PatchBOTS/L337/STLs/V2/BASE_BaseandNeck.STL

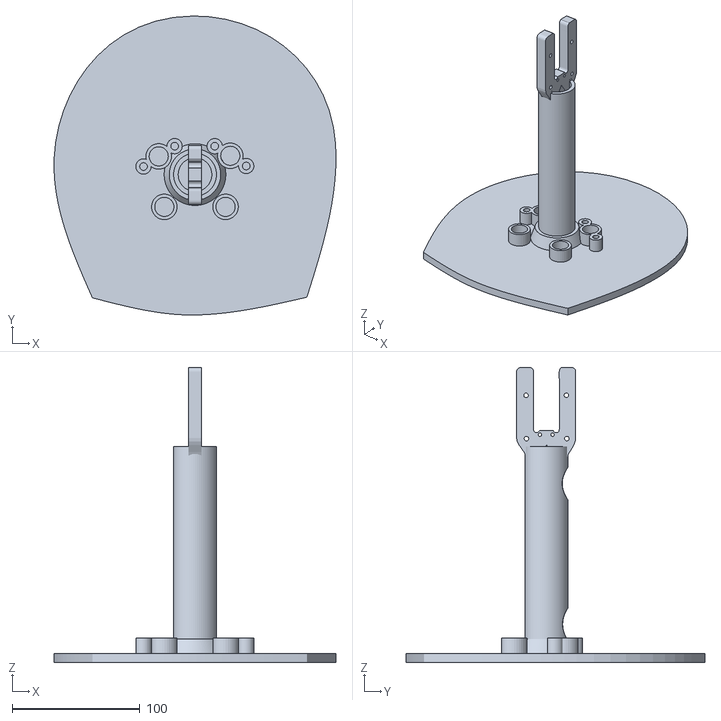
[picture p15: CAD file, 2018-09-10]
STLs/V2/BASE_BaseandNeck.STL
220.7 x 234.0 x 231.1
