PatchBOTS/L337/STLs/PartsChanging/HEAD_ELECTRICAL_MountCover.STL

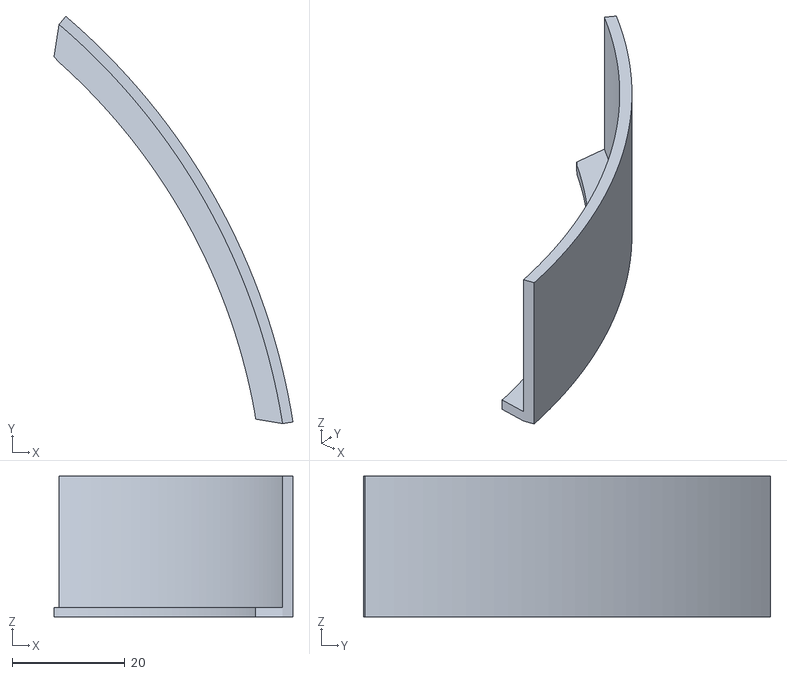
[picture p16: CAD file, 2018-06-11]
STLs/PartsChanging/HEAD_ELECTRICAL_MountCover.STL
42.4 x 72.2 x 24.9
