PatchBOTS/L337/STLs/V2/HEAD_ELECTRICAL_SpeakerMount.STL

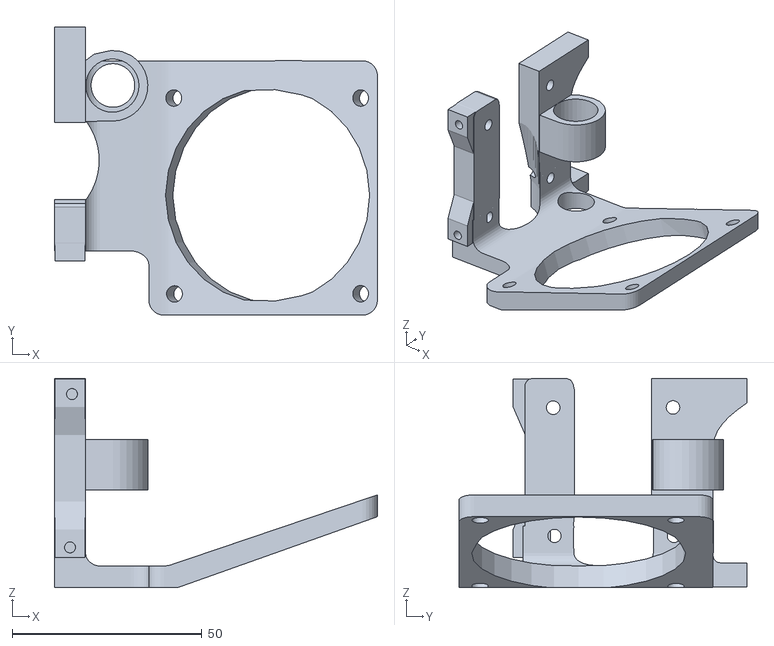
[picture p17: CAD file, 2018-09-10]
STLs/V2/HEAD_ELECTRICAL_SpeakerMount.STL
85.2 x 76.1 x 55.2
