PatchBOTS/L337/STLs/HEAD_AESTHETIC_EarGreebly.STL

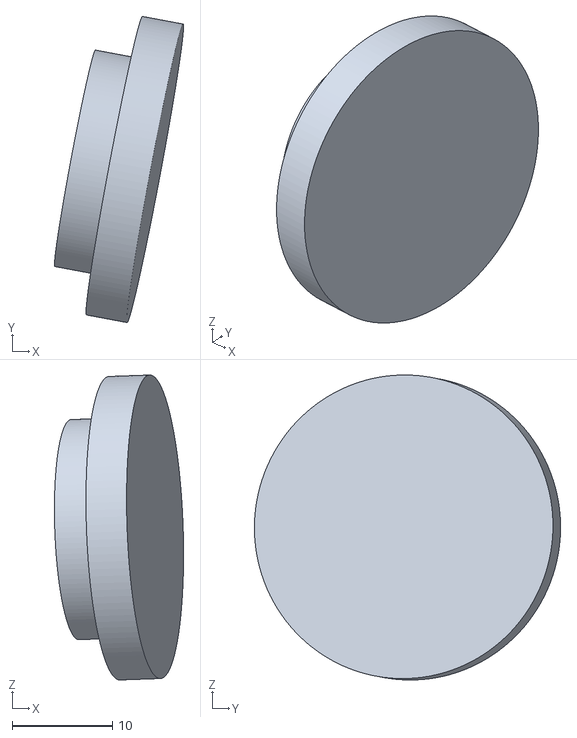
[picture p18: CAD file, 2018-06-11]
STLs/HEAD_AESTHETIC_EarGreebly.STL
12.9 x 30.5 x 30.4
