PatchBOTS/L337/STLs/HEAD_LID_Cap_T2.STL

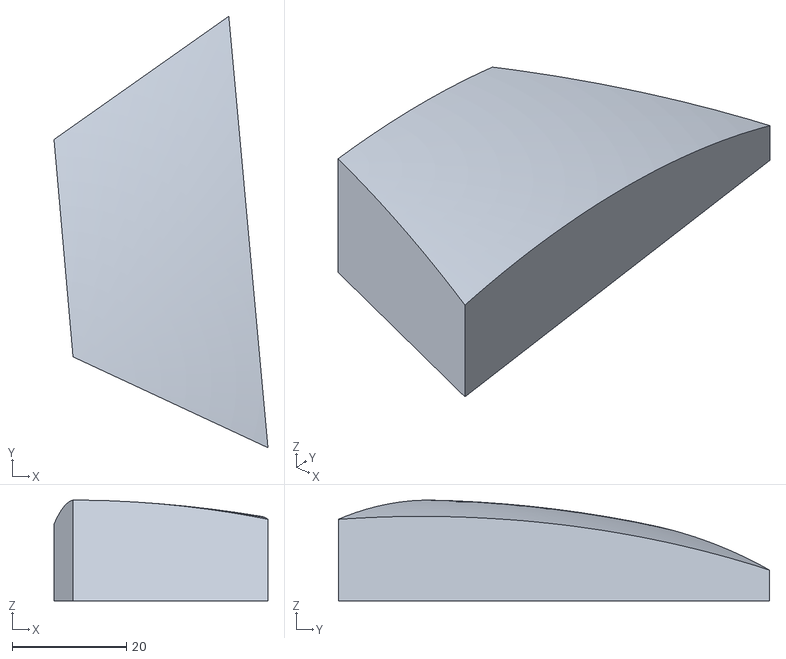
[picture p19: CAD file, 2018-06-11]
STLs/HEAD_LID_Cap_T2.STL
37.5 x 75.5 x 17.7
