PatchBOTS/L337/STLs/PartsChanging/HEAD_ELECTRICAL_InternalHoop.STL

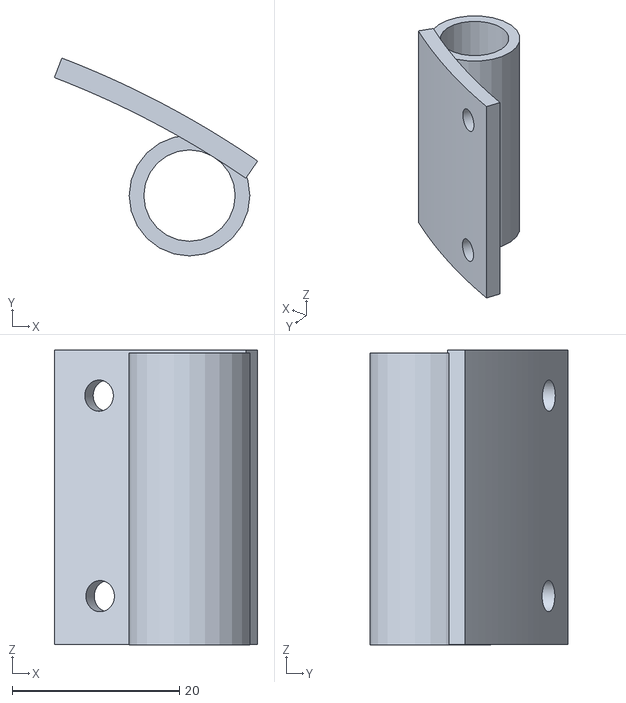
[picture p20: CAD file, 2018-06-11]
STLs/PartsChanging/HEAD_ELECTRICAL_InternalHoop.STL
24.3 x 23.7 x 35.3
