PatchBOTS/L337/STLs/HEAD_AESTHETIC_Eye.STL

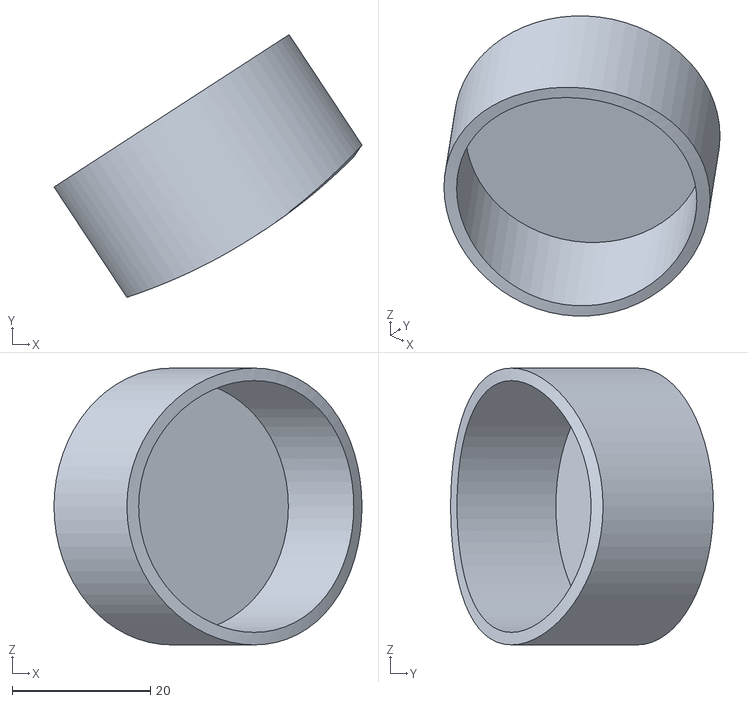
[picture p21: CAD file, 2018-06-11]
STLs/HEAD_AESTHETIC_Eye.STL
44.6 x 38.1 x 40.1
