PatchBOTS/L337/STLs/PartsChanging/HEAD_ELECTRICAL_SpeakerMount_CS.STL

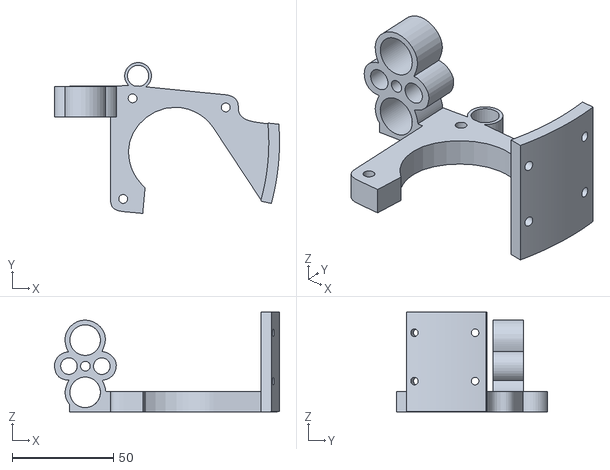
[picture p22: CAD file, 2018-06-11]
STLs/PartsChanging/HEAD_ELECTRICAL_SpeakerMount_CS.STL
111.0 x 74.5 x 49.3
