PatchBOTS/L337/STLs/HEAD_LID_Cap_T1.STL

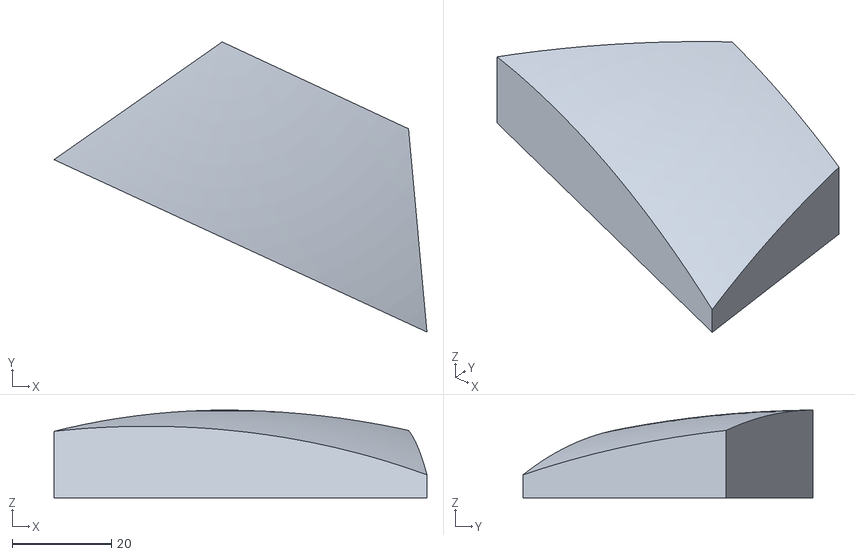
[picture p23: CAD file, 2018-06-11]
STLs/HEAD_LID_Cap_T1.STL
75.2 x 58.5 x 17.7
