PatchBOTS/L337/STLs/BASE_CollarGreebly.STL

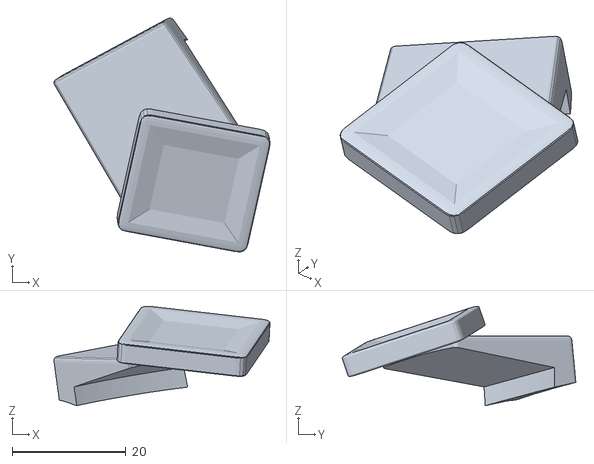
[picture p24: CAD file, 2018-06-11]
STLs/BASE_CollarGreebly.STL
38.0 x 41.2 x 17.5
