PatchBOTS/L337/STLs/HEAD_LID_Cap_T3.STL

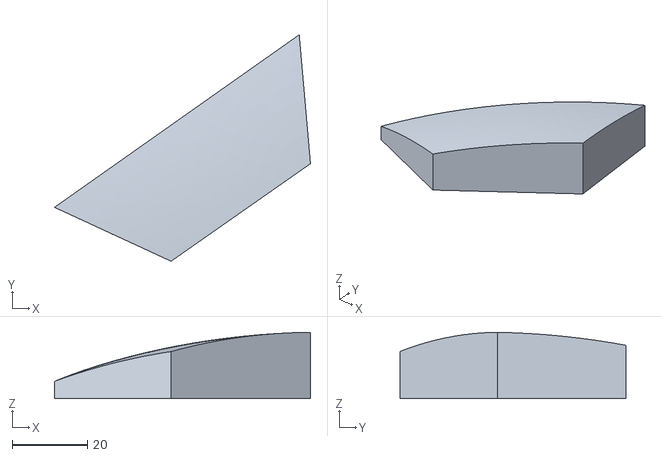
[picture p25: CAD file, 2018-06-11]
STLs/HEAD_LID_Cap_T3.STL
68.0 x 60.2 x 17.6
