PatchBOTS/L337/STLs/HEAD_ELECTRICAL_NeoDiffusex2.STL

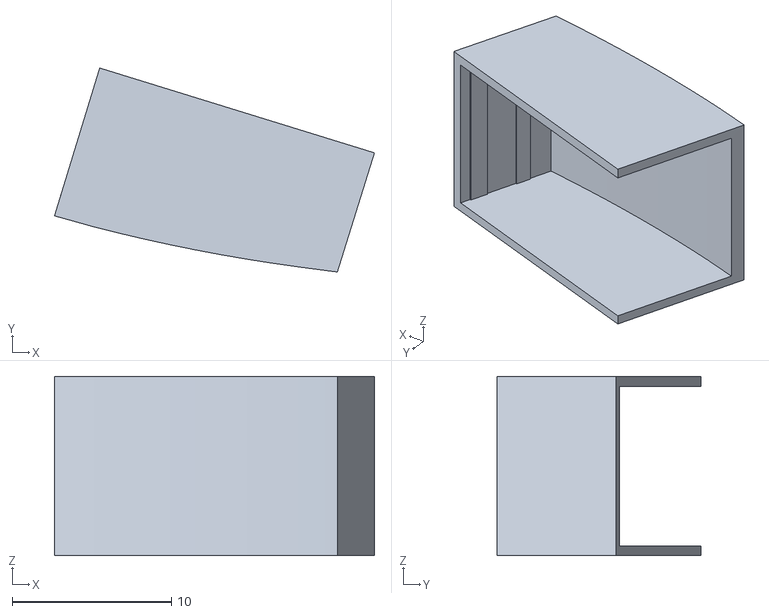
[picture p26: CAD file, 2018-06-11]
STLs/HEAD_ELECTRICAL_NeoDiffusex2.STL
20.1 x 12.8 x 11.3
