PatchBOTS/L337/STLs/HEAD_LID_Base.STL

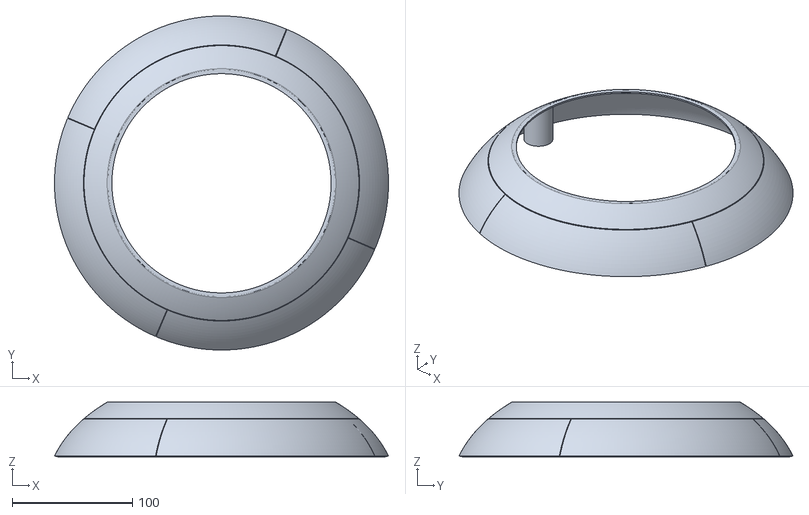
[picture p27: CAD file, 2018-06-11]
STLs/HEAD_LID_Base.STL
278.0 x 278.0 x 45.4
