PatchBOTS/L337/STLs/HEAD_LID_Cap_Holo.STL

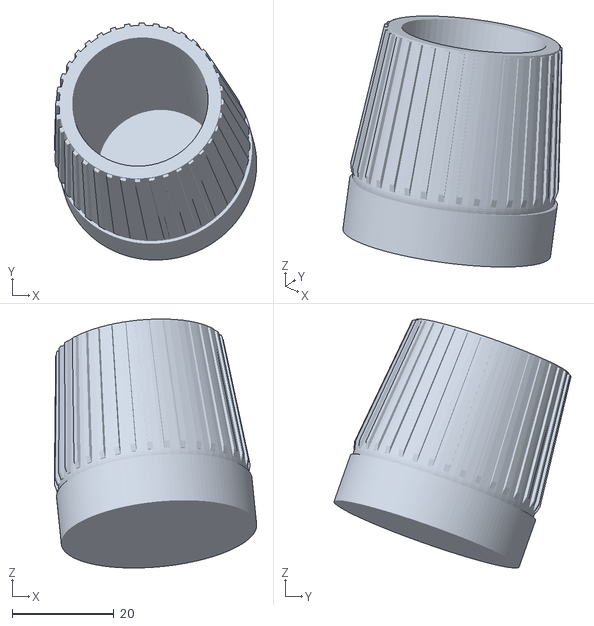
[picture p28: CAD file, 2018-06-11]
STLs/HEAD_LID_Cap_Holo.STL
39.9 x 46.7 x 49.1
