PatchBOTS/L337/STLs/ANTENNA_Ring.STL

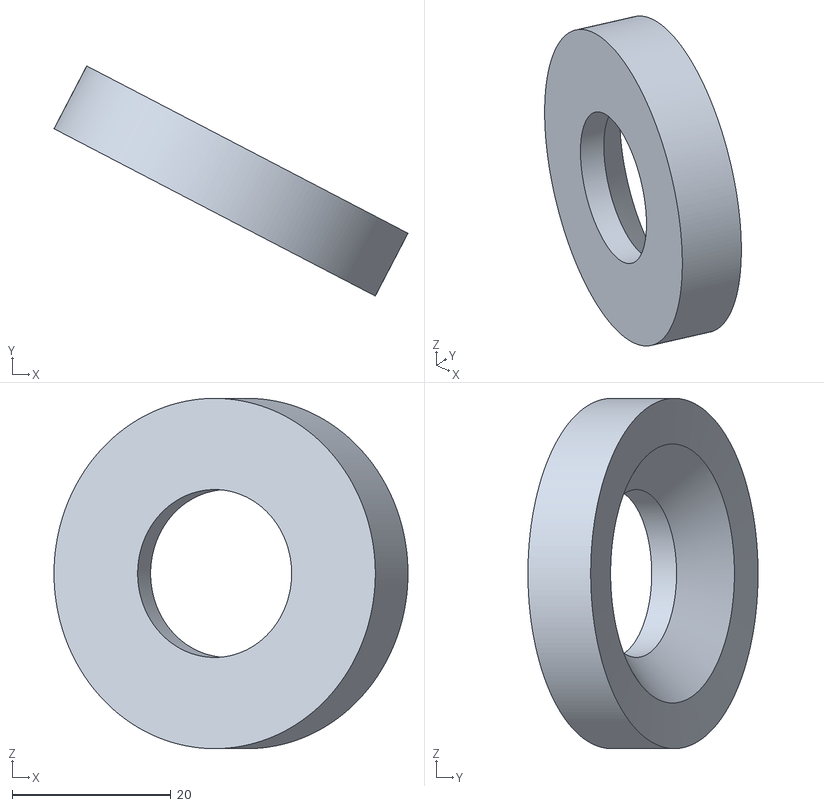
[picture p29: CAD file, 2018-06-11]
STLs/ANTENNA_Ring.STL
44.6 x 29.0 x 44.1
