PatchBOTS/L337/STLs/HEAD_AESTHETIC_MouthGreebly.STL

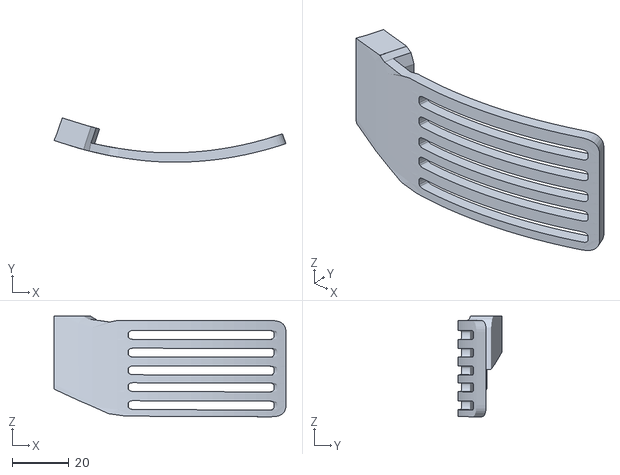
[picture p30: CAD file, 2018-06-11]
STLs/HEAD_AESTHETIC_MouthGreebly.STL
81.6 x 15.6 x 35.4
