PatchBOTS/L337/STLs/HEAD_AESTHETIC_EyeLid.STL

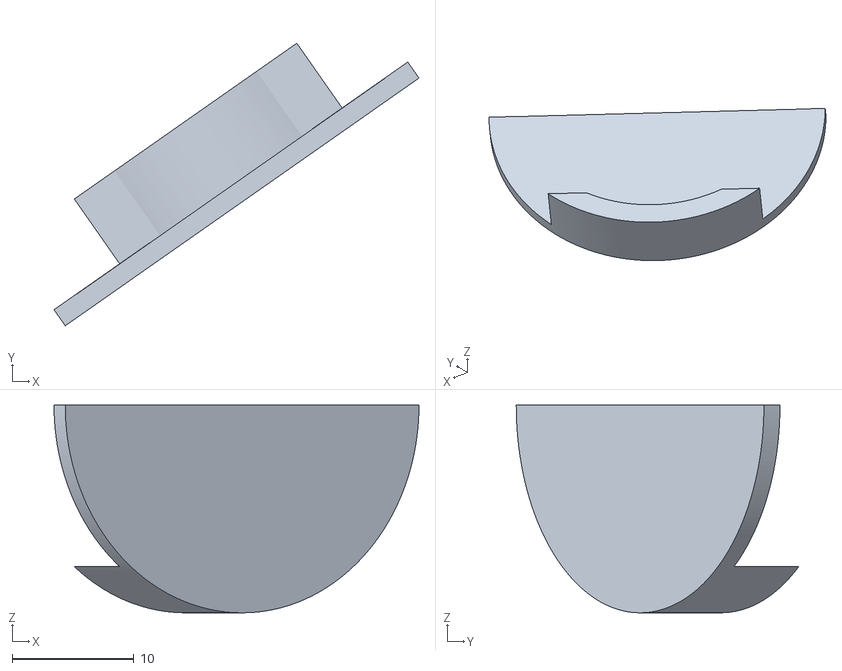
[picture p31: CAD file, 2018-06-11]
STLs/HEAD_AESTHETIC_EyeLid.STL
30.0 x 23.2 x 17.1
