PatchBOTS/L337/STLs/BASE_WireGrommit.STL

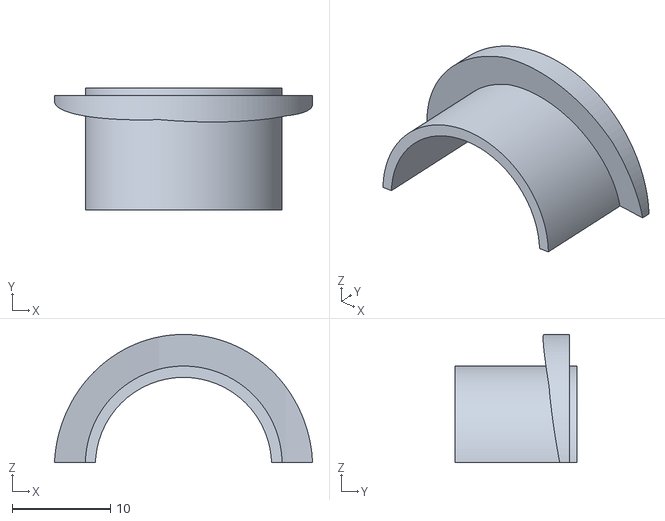
[picture p32: CAD file, 2018-06-11]
STLs/BASE_WireGrommit.STL
26.3 x 12.4 x 13.1
