PatchBOTS/L337/STLs/HEAD_AESTHETIC_VisorGreebly.STL

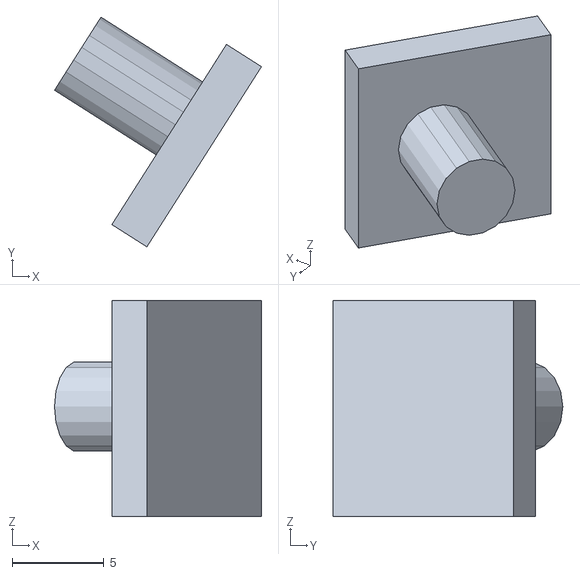
[picture p33: CAD file, 2018-06-11]
STLs/HEAD_AESTHETIC_VisorGreebly.STL
11.3 x 12.5 x 11.8
