PatchBOTS/L337/STLs/BASE_Collar.STL

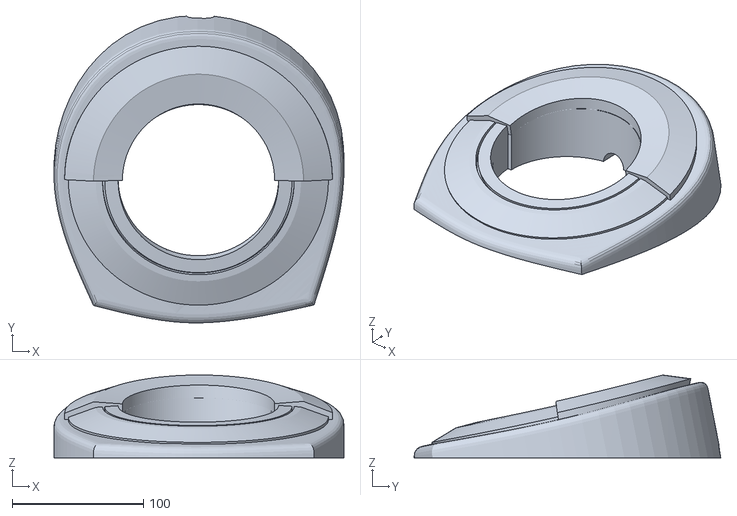
[picture p34: CAD file, 2018-06-11]
STLs/BASE_Collar.STL
220.7 x 233.4 x 63.1
