PatchBOTS/L337/STLs/HEAD_ELECTRICAL_NeoPixelHolder.STL

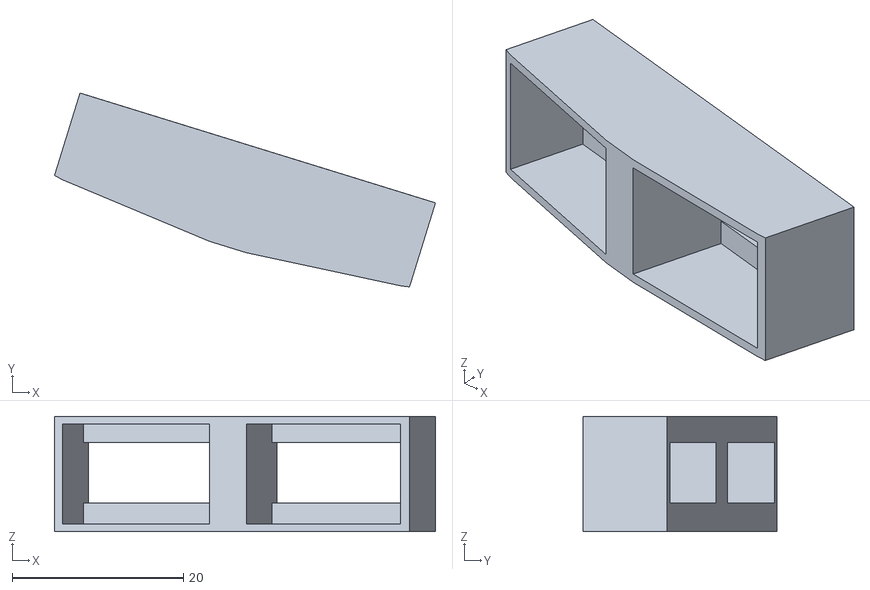
[picture p35: CAD file, 2018-06-11]
STLs/HEAD_ELECTRICAL_NeoPixelHolder.STL
44.5 x 22.6 x 13.4
